freillyskis-coder/Telemetry-Macropad/Telemetry Hackpad/Images/Current Designs/Assembly Rear View 4.png

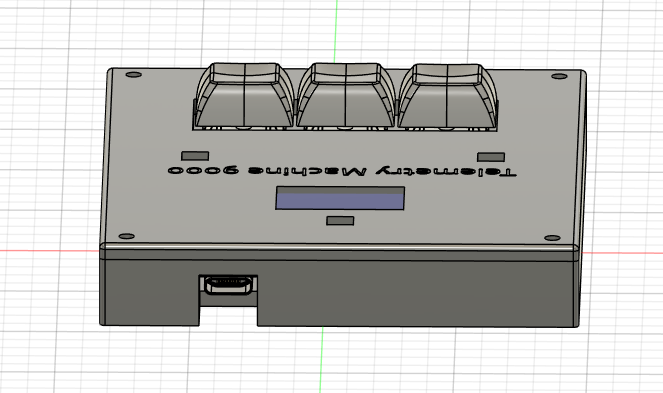
Telemetry Hackpad/Images/Current Designs/Assembly Rear View 4.png
