freillyskis-coder/Telemetry-Macropad/Telemetry Hackpad/Images/Current Designs/Assembly Top View 4.png

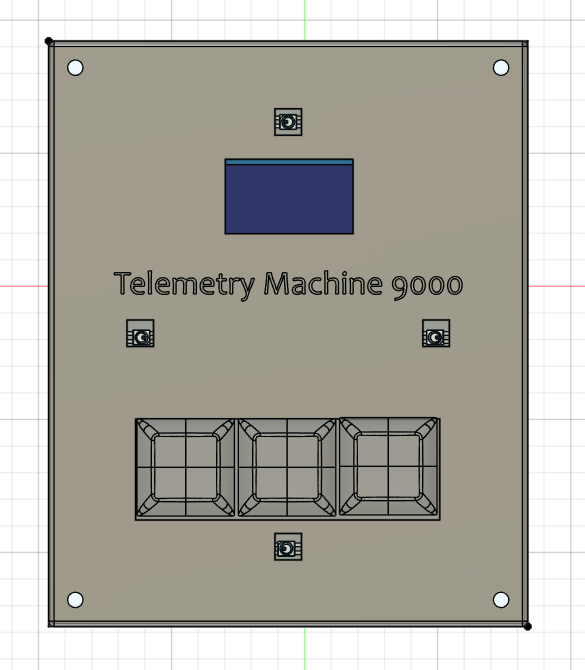
Telemetry Hackpad/Images/Current Designs/Assembly Top View 4.png
